bytesbrains/lvc-dream-cube/kickstarter/reward-images/buy-one-give-one.jpg

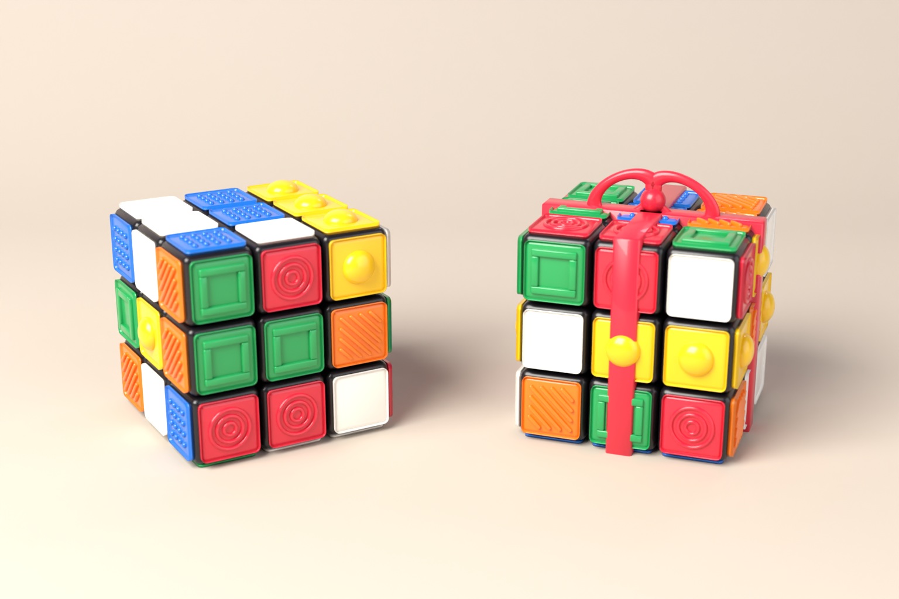
kickstarter/reward-images/buy-one-give-one.jpg
