bytesbrains/lvc-dream-cube/kickstarter/reward-images/chip-kit.jpg

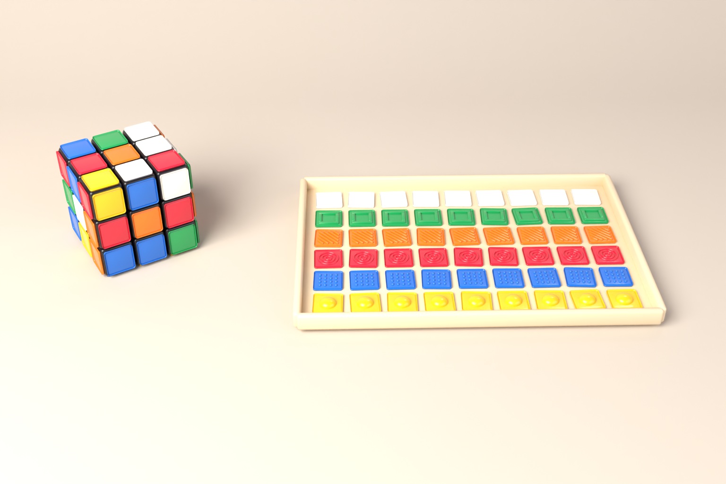
kickstarter/reward-images/chip-kit.jpg
