bytesbrains/lvc-dream-cube/kickstarter/reward-images/dream-cube.jpg

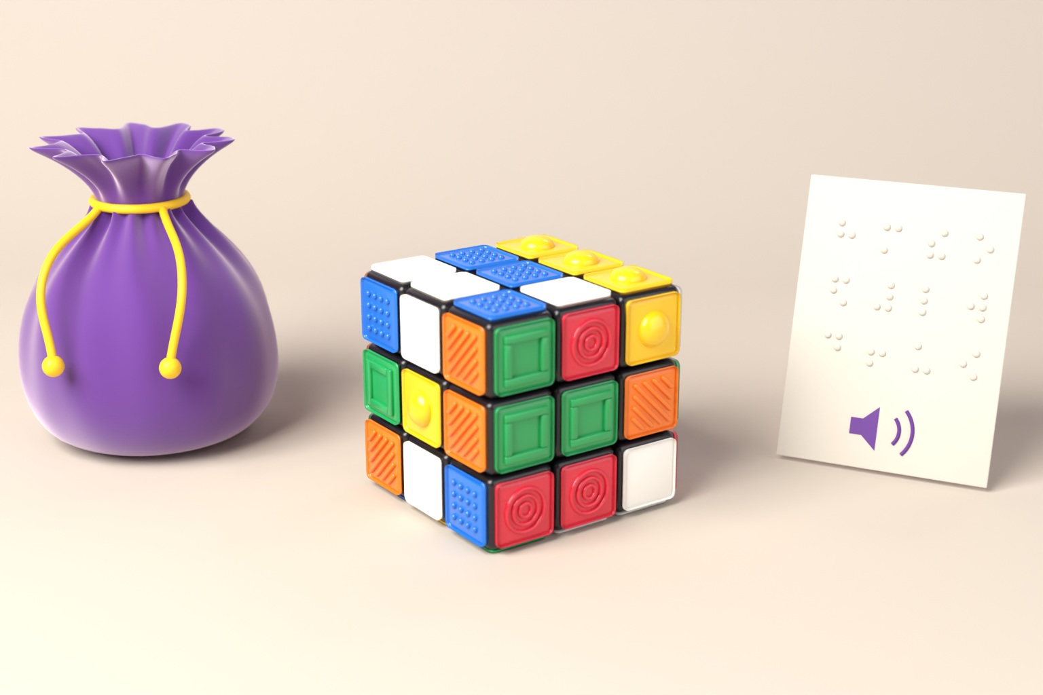
kickstarter/reward-images/dream-cube.jpg
