bytesbrains/lvc-dream-cube/kickstarter/reward-images/give-a-cube.jpg

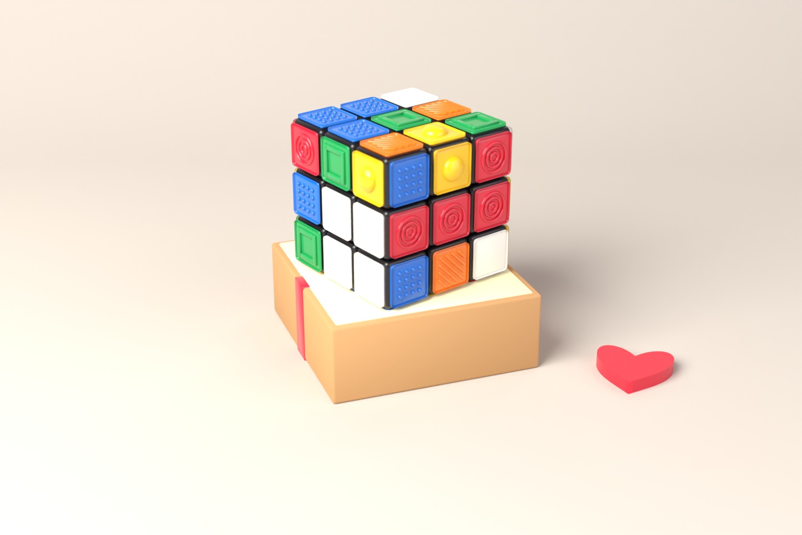
kickstarter/reward-images/give-a-cube.jpg
