bytesbrains/lvc-dream-cube/kickstarter/reward-images/item-chip-kit.jpg

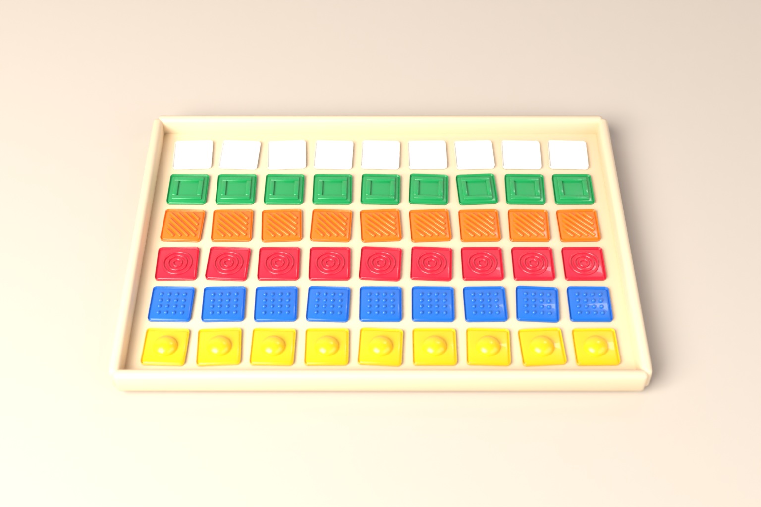
kickstarter/reward-images/item-chip-kit.jpg
