bytesbrains/lvc-dream-cube/kickstarter/reward-images/item-dream-cube.jpg

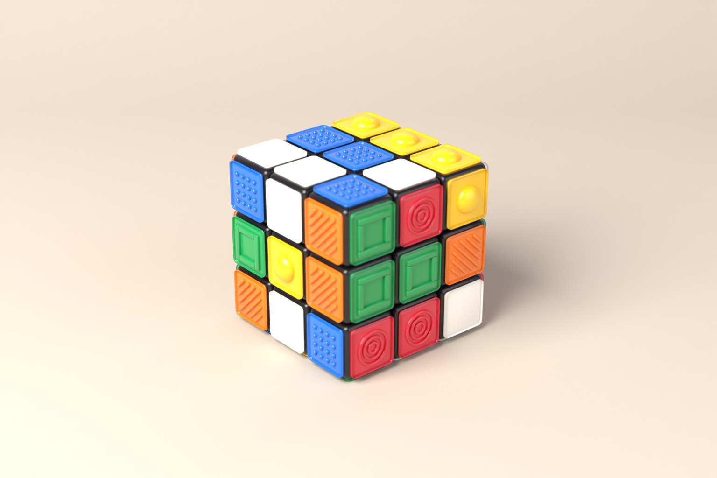
kickstarter/reward-images/item-dream-cube.jpg
