bytesbrains/lvc-dream-cube/kickstarter/reward-images/item-name-in-credits.jpg

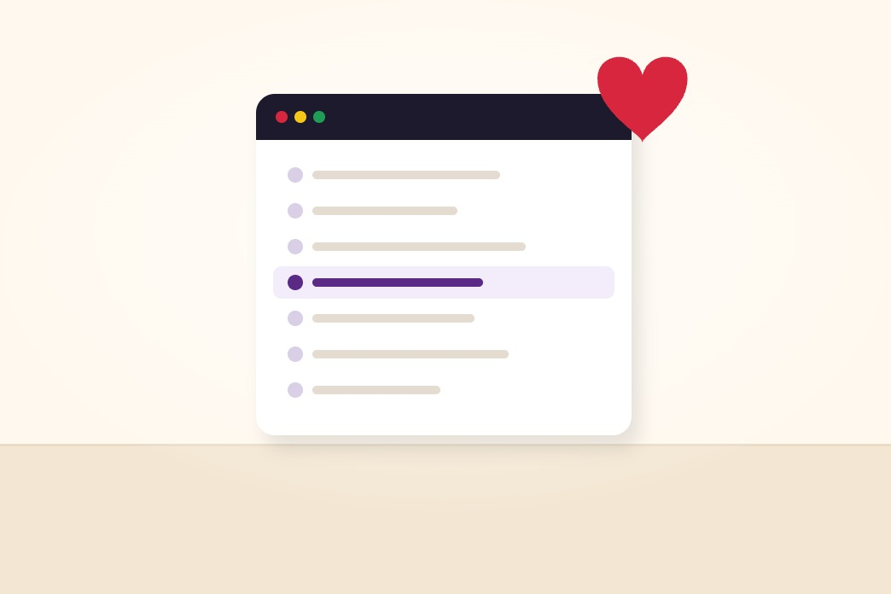
kickstarter/reward-images/item-name-in-credits.jpg
