bytesbrains/lvc-dream-cube/kickstarter/reward-images/school-ngo-pack.jpg

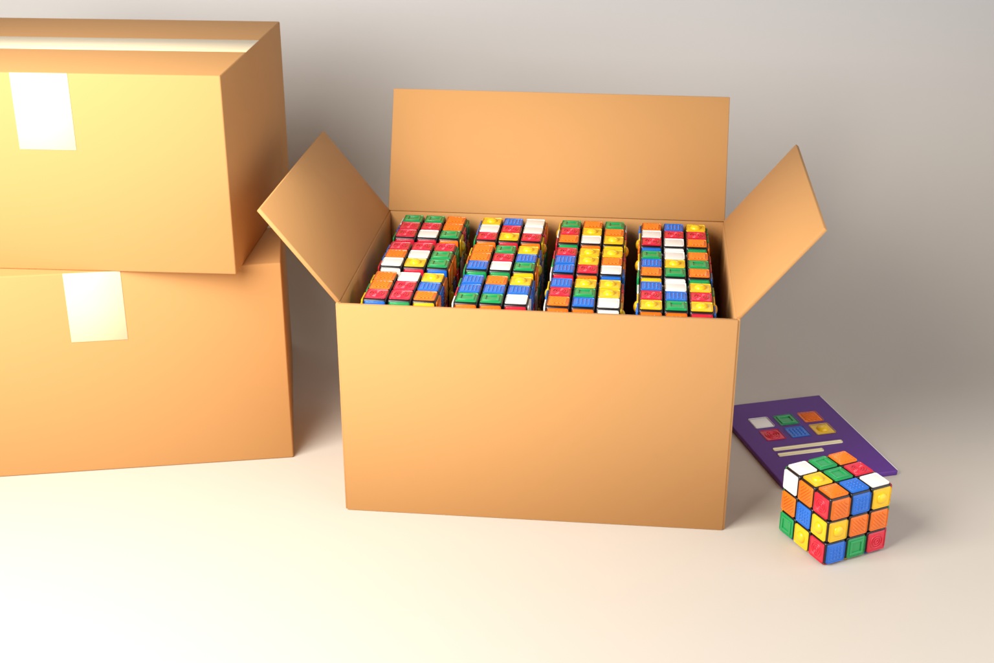
kickstarter/reward-images/school-ngo-pack.jpg
