bytesbrains/lvc-dream-cube/kickstarter/reward-images/school-starter.jpg

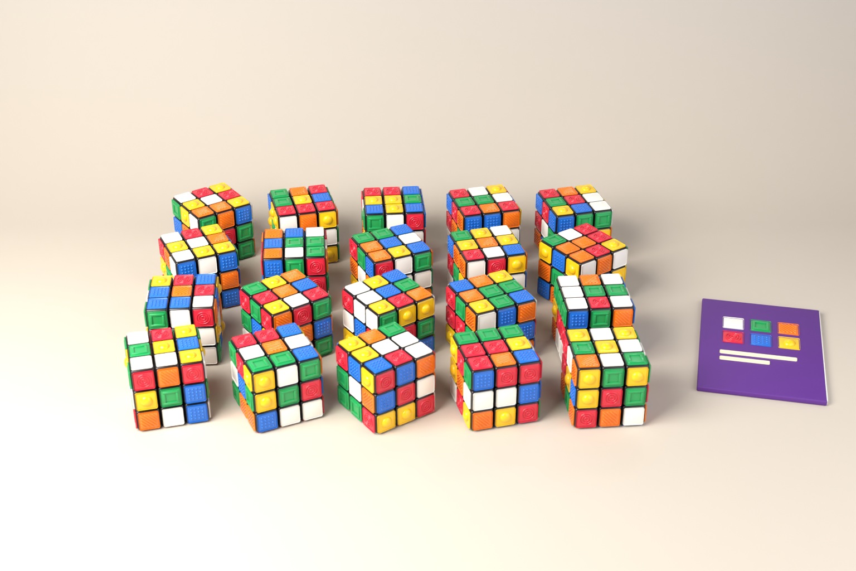
kickstarter/reward-images/school-starter.jpg
