bytesbrains/lvc-dream-cube/kickstarter/reward-images/supporter.jpg

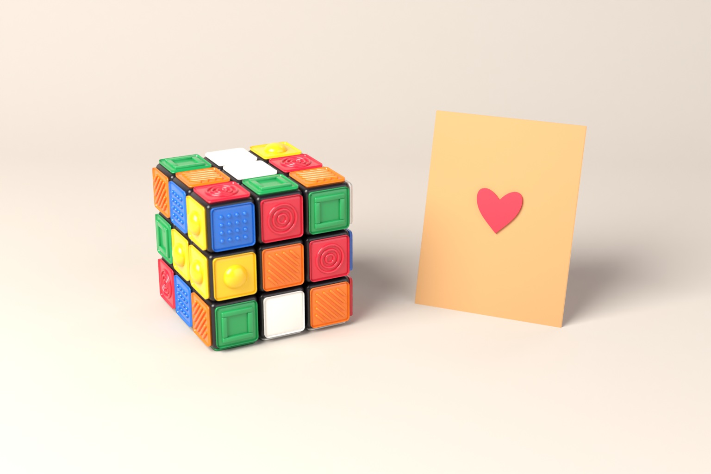
kickstarter/reward-images/supporter.jpg
