bytesbrains/lvc-dream-cube/kickstarter/social/just-launched-instagram.jpg

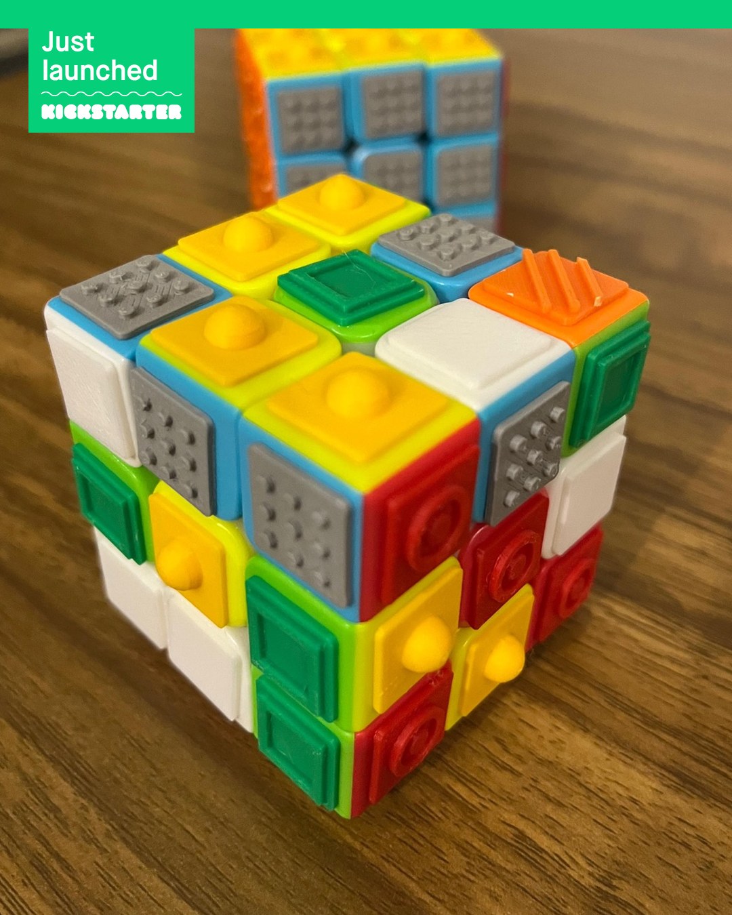
kickstarter/social/just-launched-instagram.jpg
